vandjac/Logic-PCB/Screenshots/Logic-PCB-Front.png

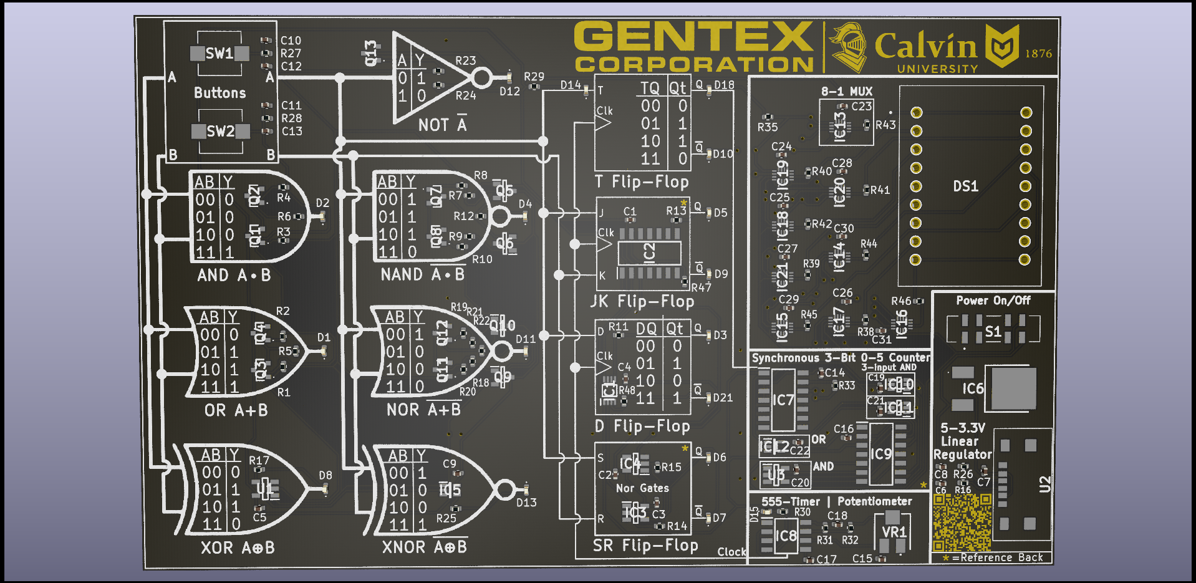
Screenshots/Logic-PCB-Front.png
