vandjac/Logic-PCB/Screenshots/AND.PNG

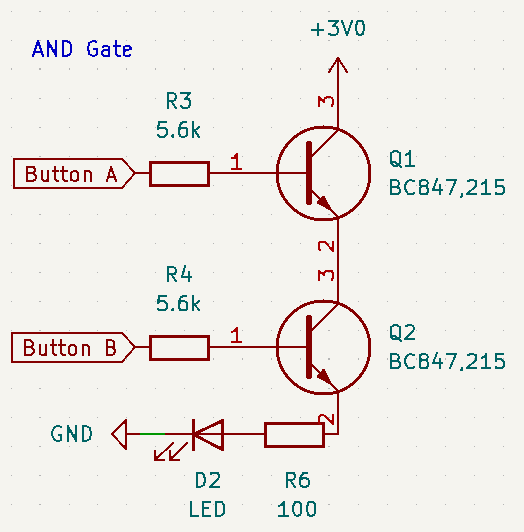
Screenshots/AND.PNG
