vandjac/Logic-PCB/Screenshots/Battery.PNG

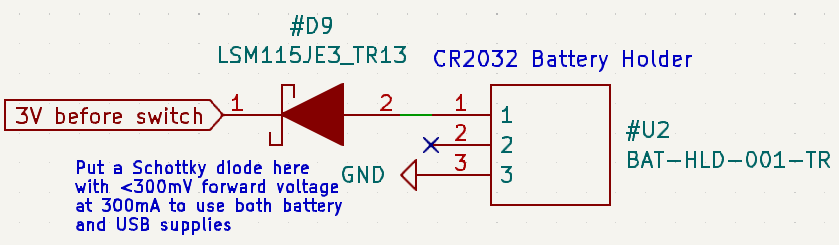
Screenshots/Battery.PNG
