vandjac/Logic-PCB/Screenshots/Buttons.PNG

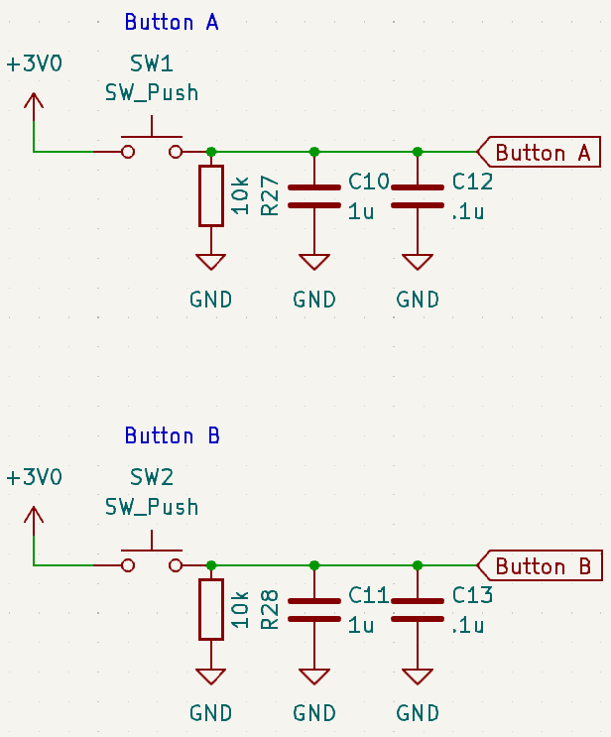
Screenshots/Buttons.PNG
