vandjac/Logic-PCB/Screenshots/Clock.PNG

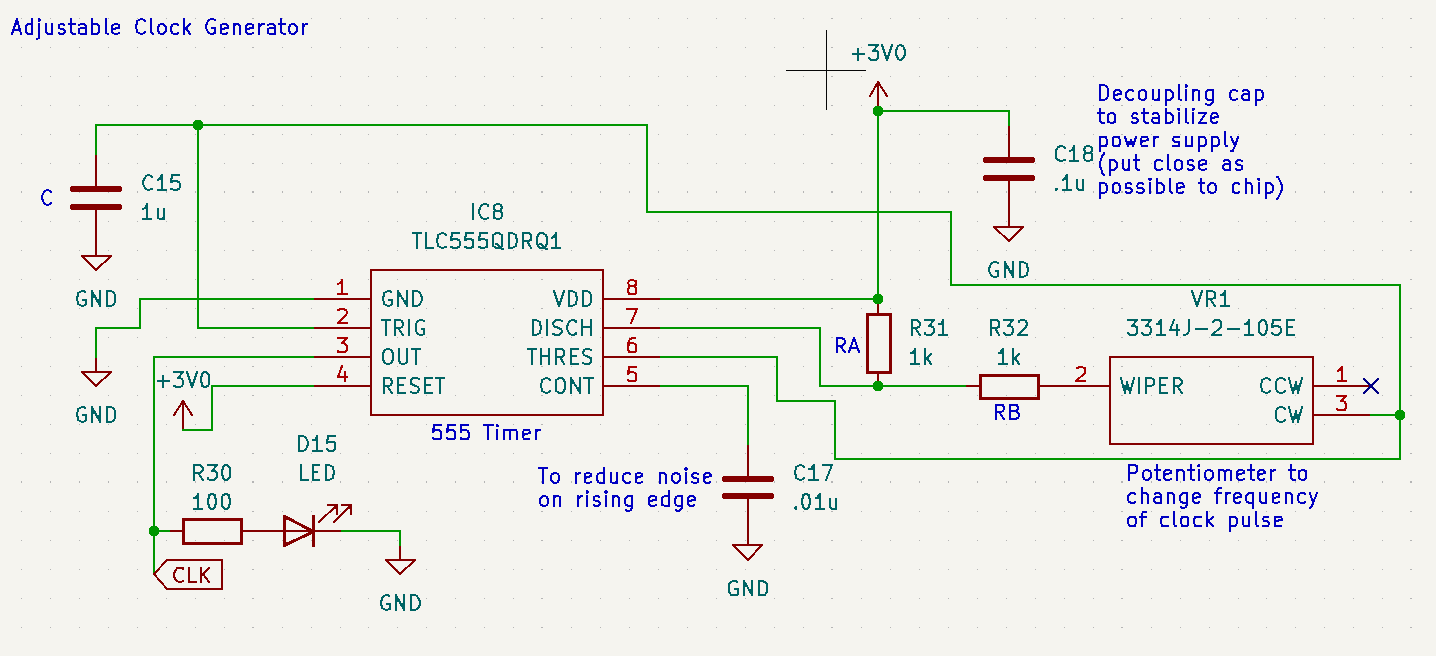
Screenshots/Clock.PNG
