vandjac/Logic-PCB/Screenshots/Counter.PNG

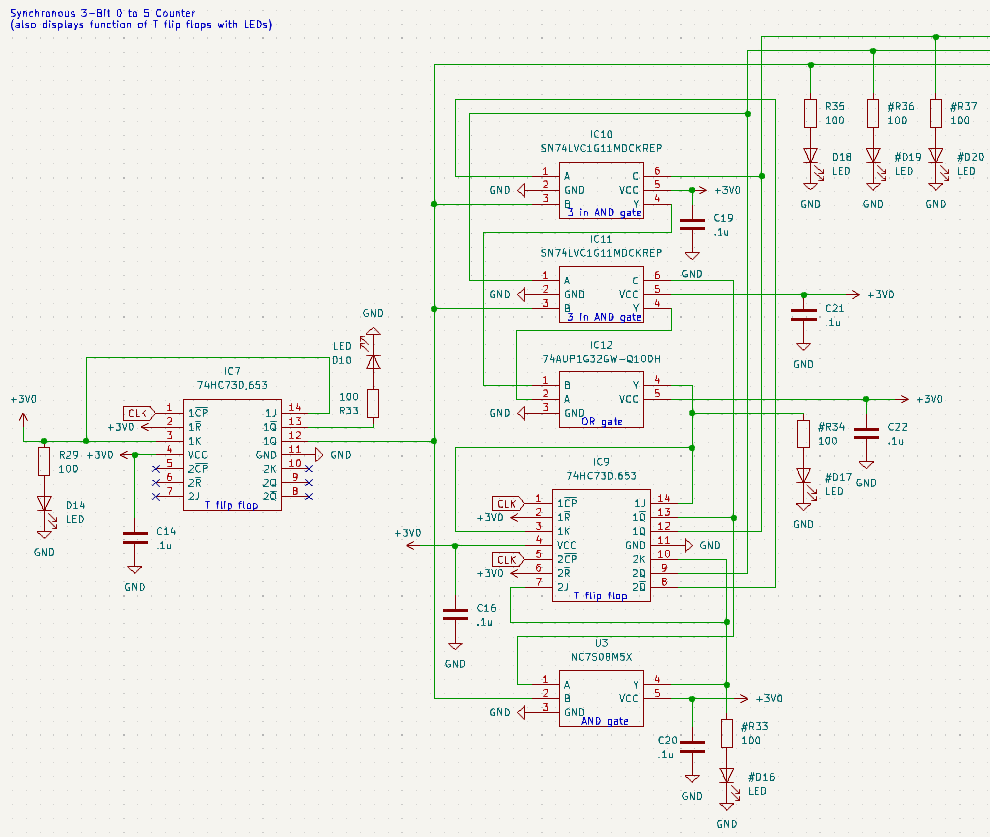
Screenshots/Counter.PNG
