vandjac/Logic-PCB/Screenshots/CounterSim.PNG

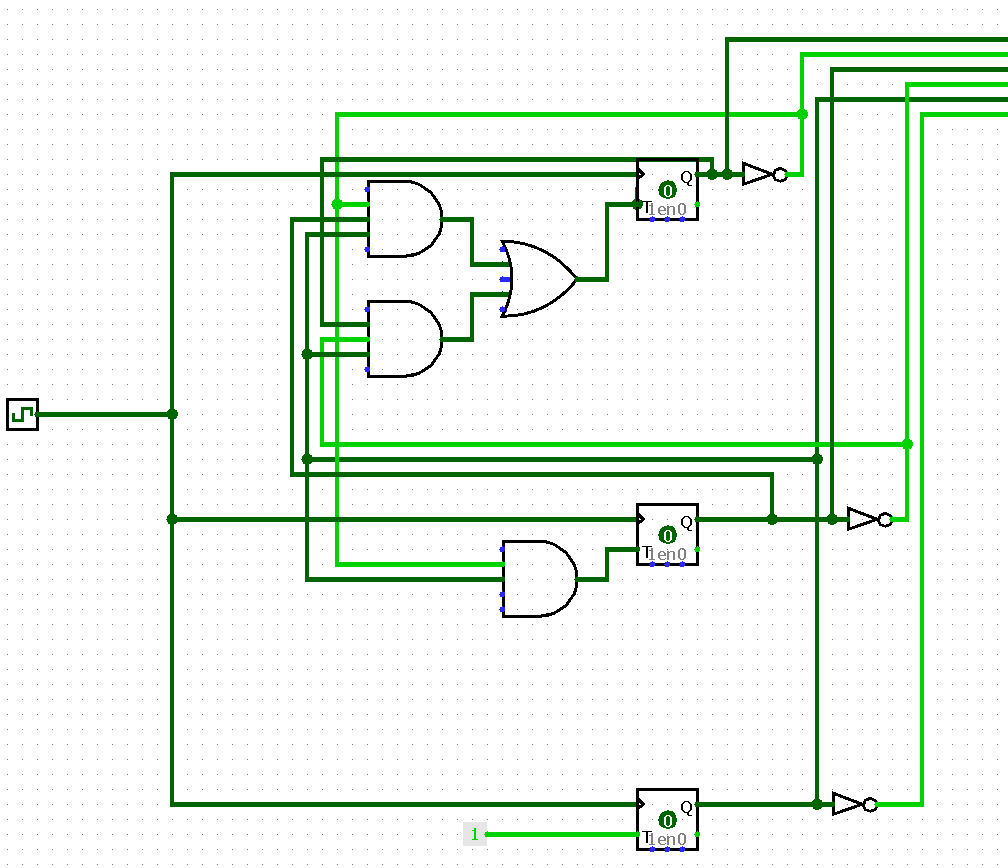
Screenshots/CounterSim.PNG
