vandjac/Logic-PCB/Screenshots/D flip flop.PNG

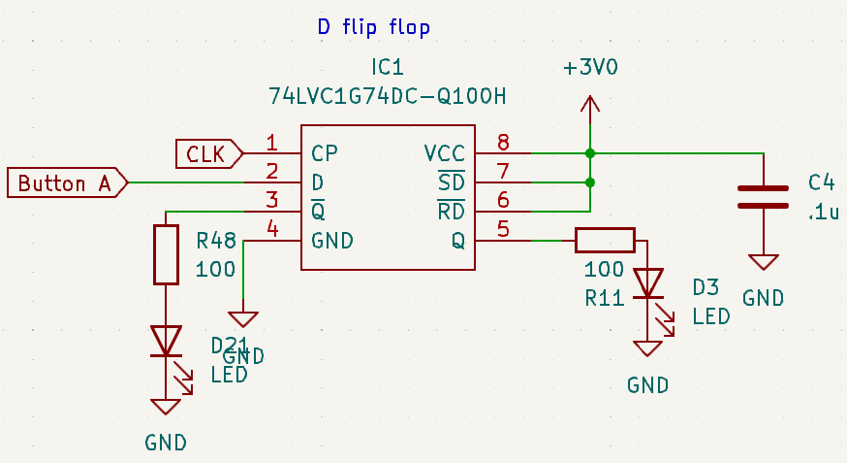
Screenshots/D flip flop.PNG
