vandjac/Logic-PCB/Screenshots/Logic_PCB_Layout_Back.png

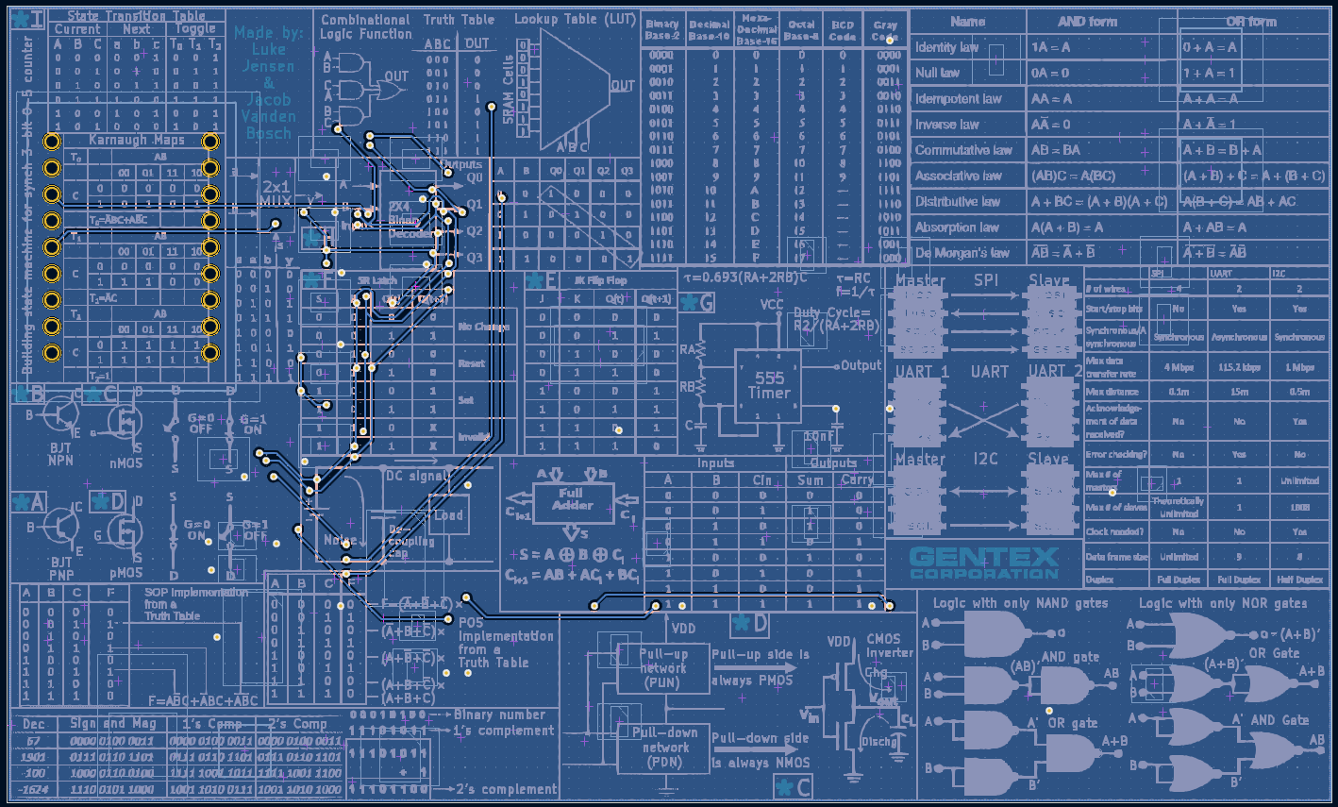
Screenshots/Logic_PCB_Layout_Back.png
