vandjac/Logic-PCB/Screenshots/Logic_PCB_Layout_Front.png

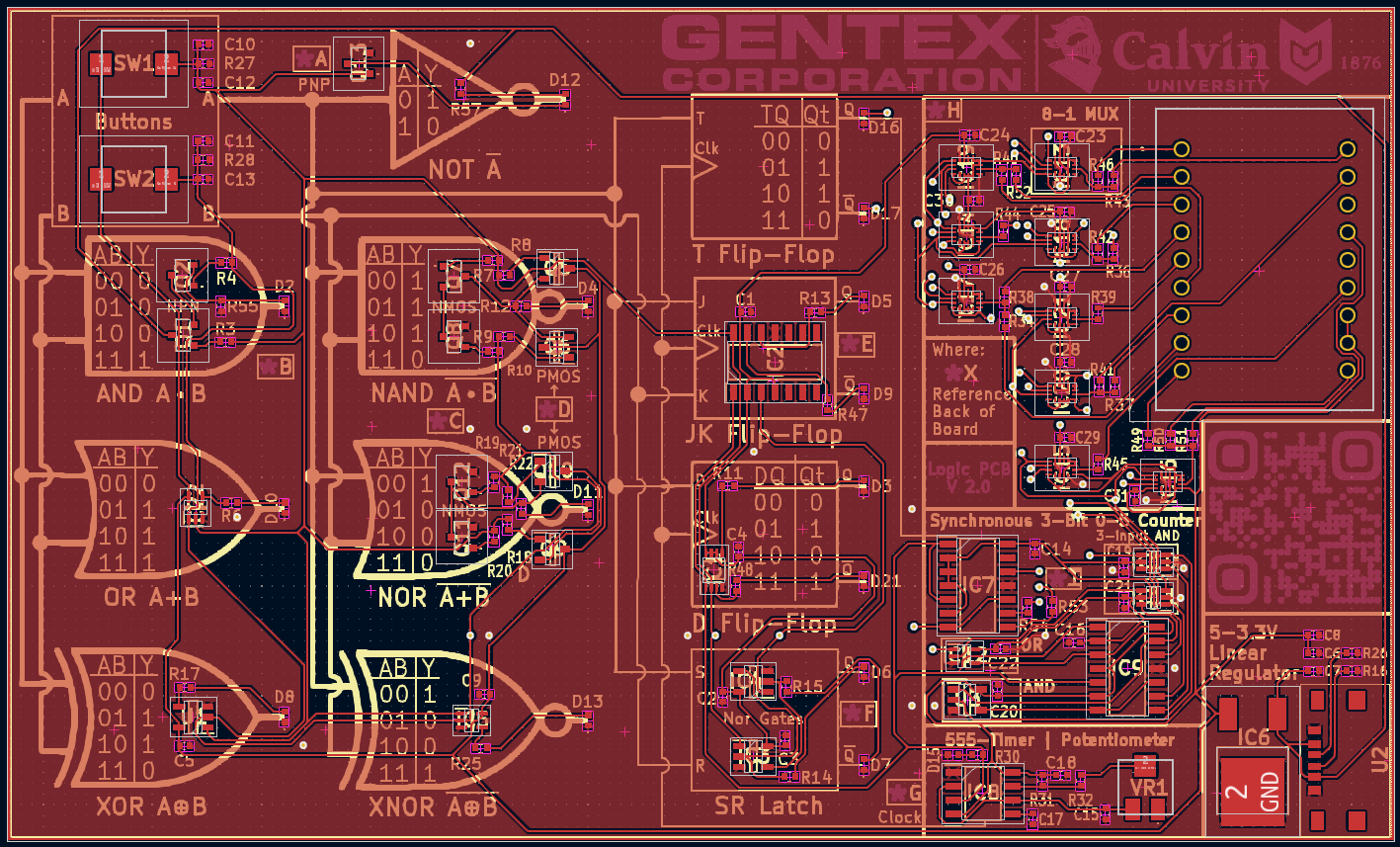
Screenshots/Logic_PCB_Layout_Front.png
