vandjac/Logic-PCB/Screenshots/Logic_PCB_Routing_Back.png

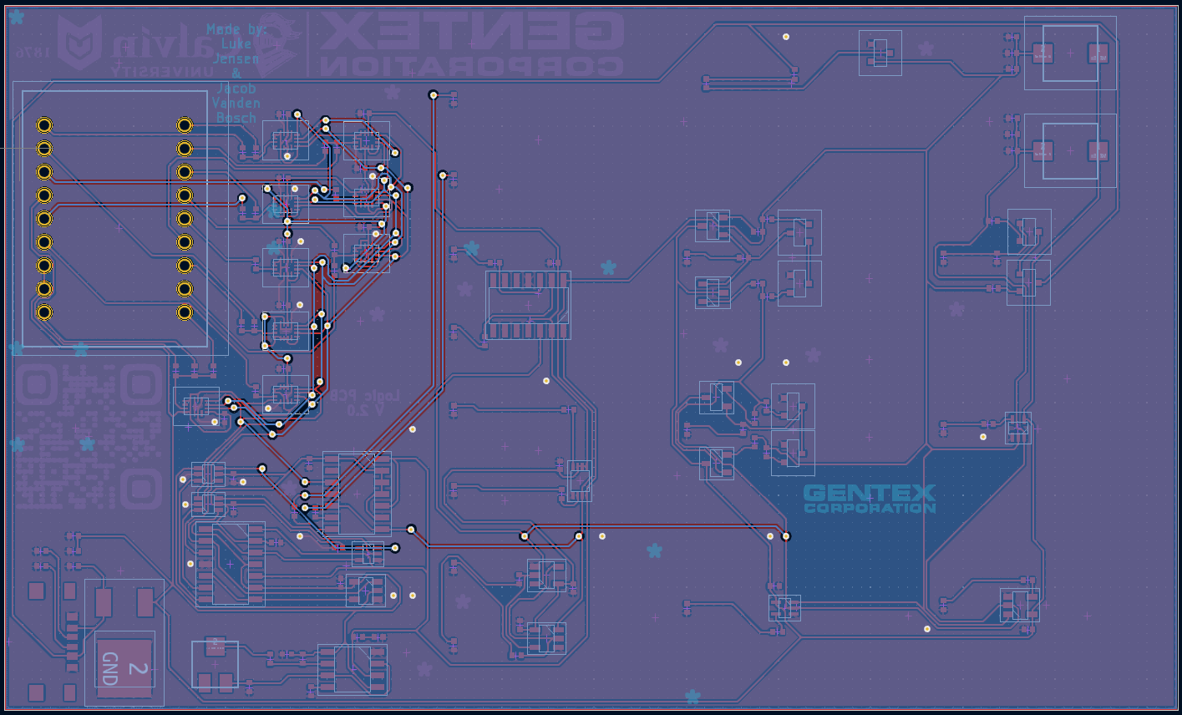
Screenshots/Logic_PCB_Routing_Back.png
