vandjac/Logic-PCB/Screenshots/Logic_PCB_Routing_Front.png

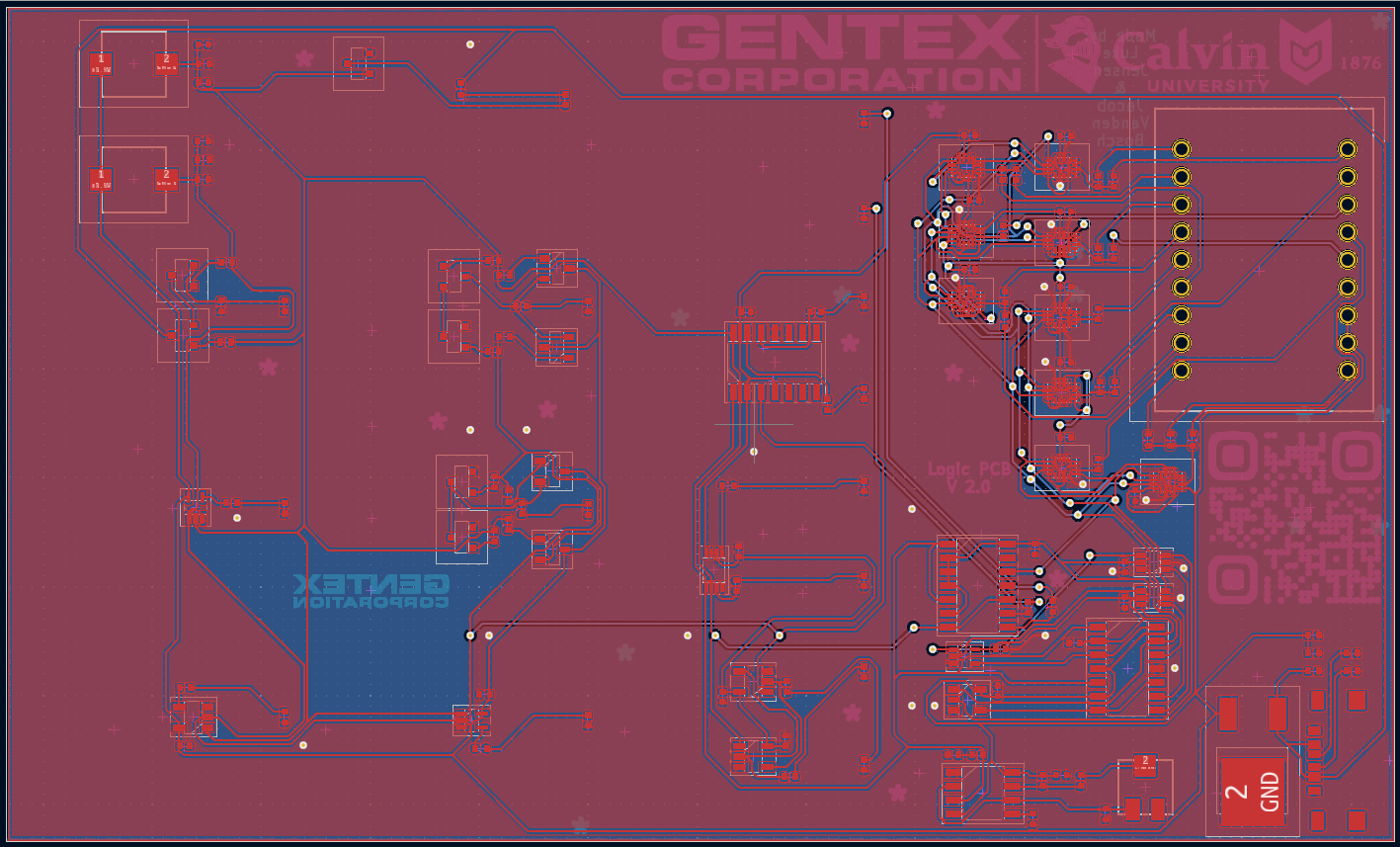
Screenshots/Logic_PCB_Routing_Front.png
