vandjac/Logic-PCB/Screenshots/Muxes.PNG

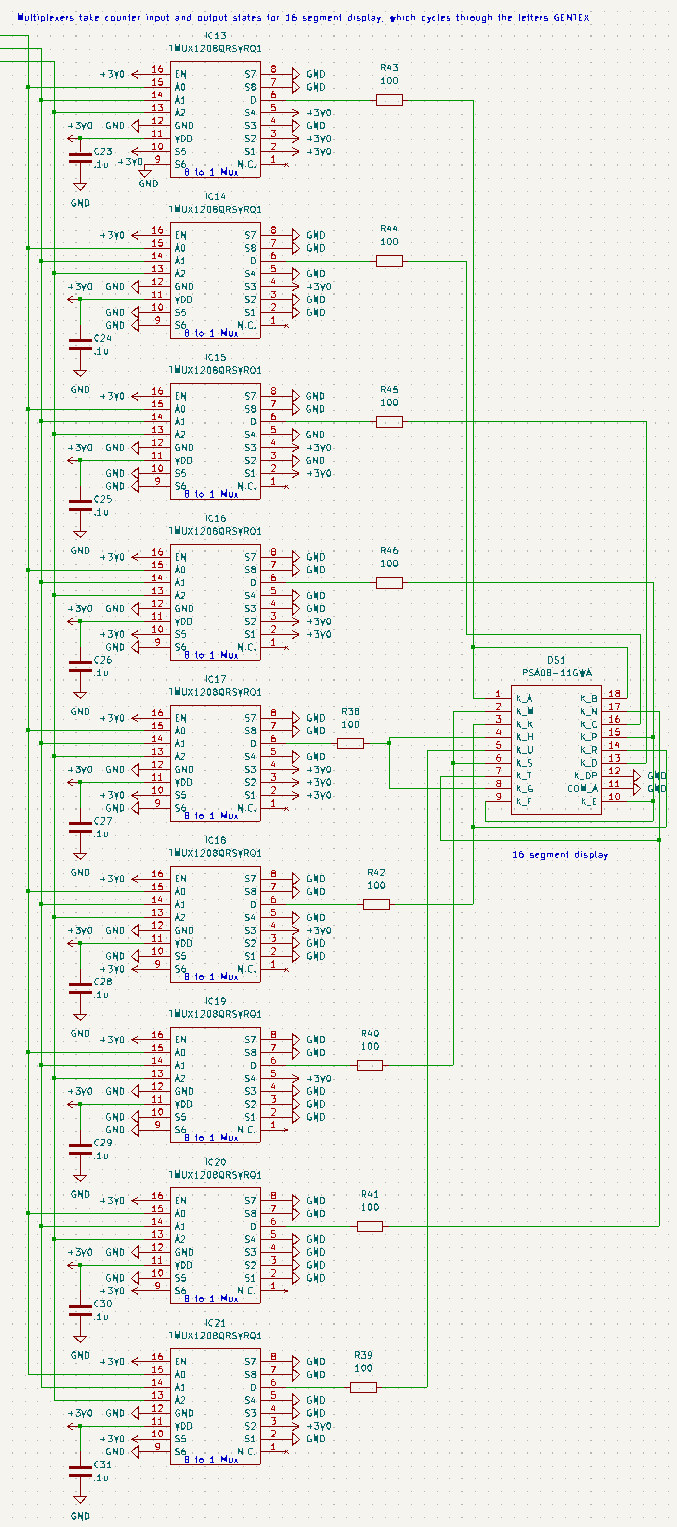
Screenshots/Muxes.PNG
