vandjac/Logic-PCB/Screenshots/NAND.PNG

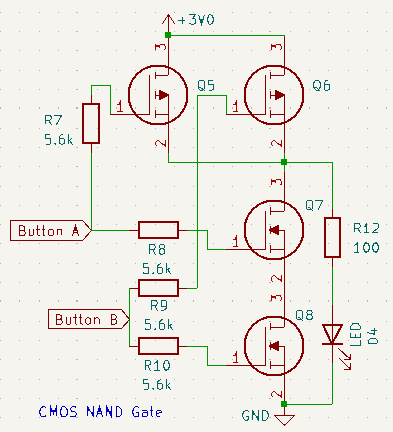
Screenshots/NAND.PNG
