vandjac/Logic-PCB/Screenshots/NOR.PNG

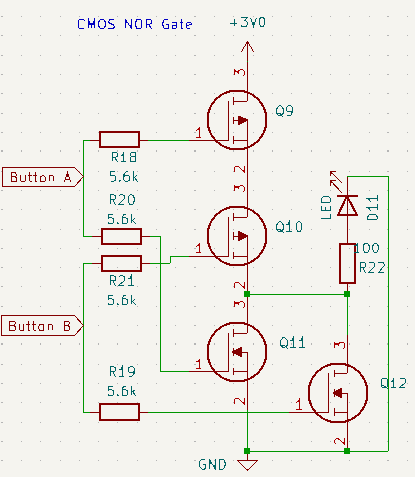
Screenshots/NOR.PNG
