vandjac/Logic-PCB/Screenshots/On Off switch.PNG

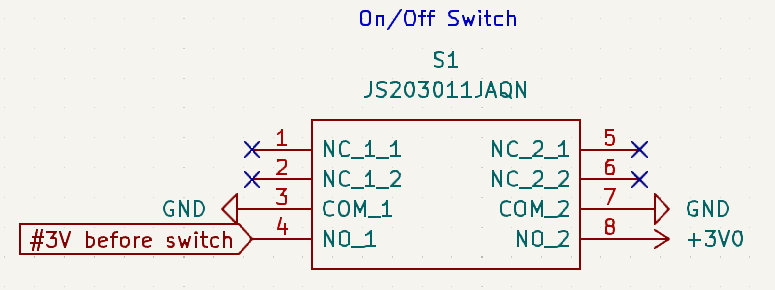
Screenshots/On Off switch.PNG
