vandjac/Logic-PCB/Screenshots/Sim.png

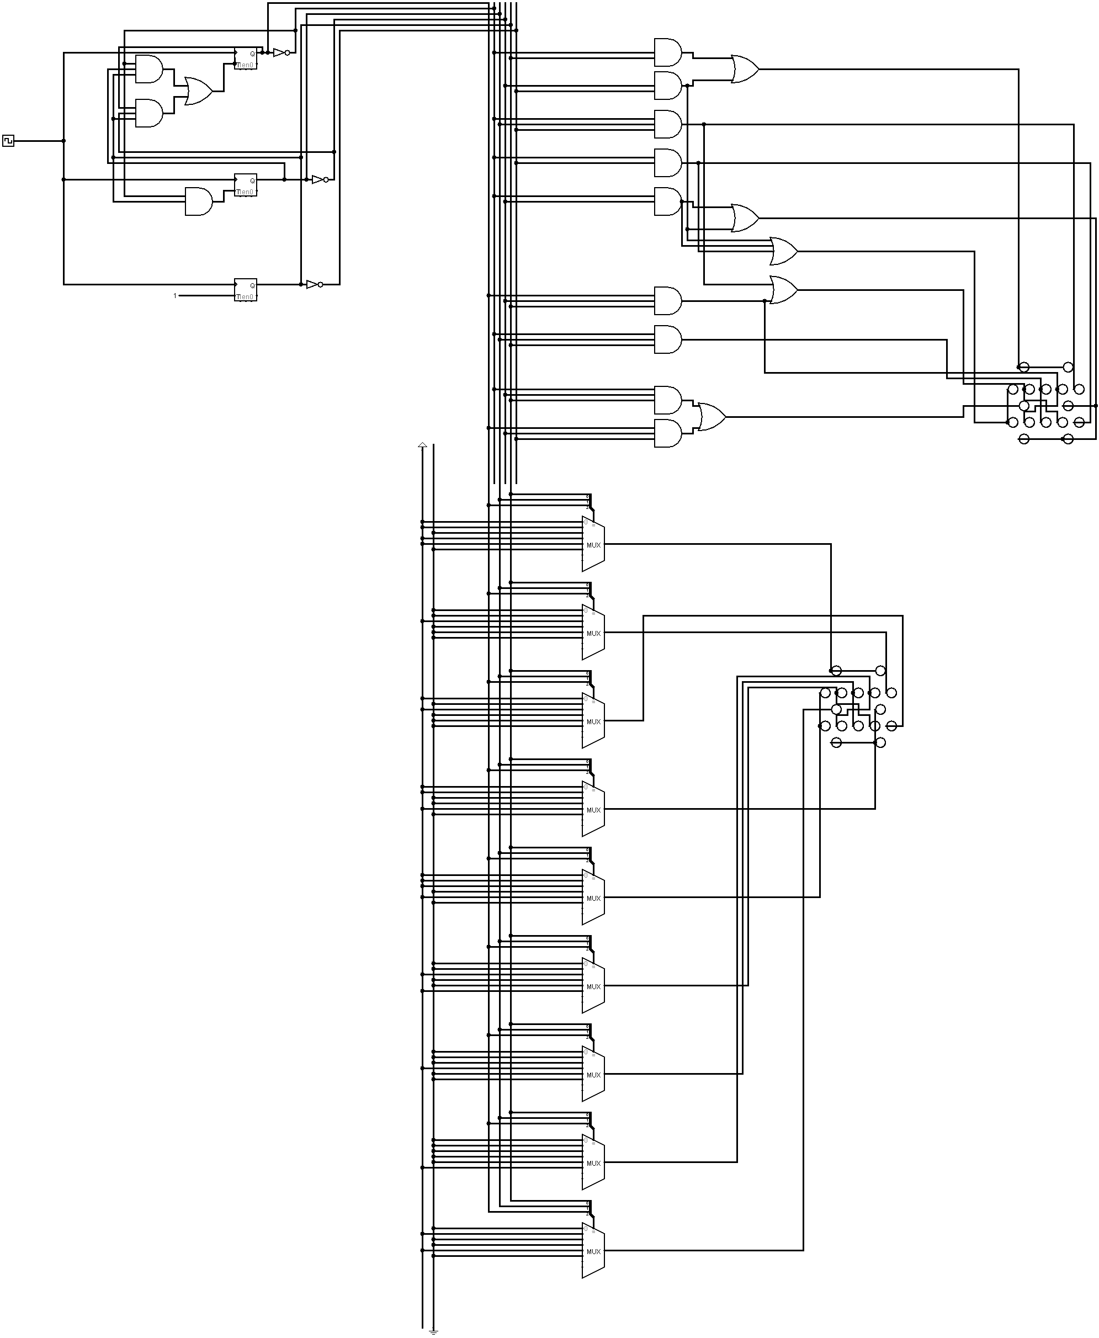
Screenshots/Sim.png
