vandjac/Logic-PCB/Screenshots/SR latch.PNG

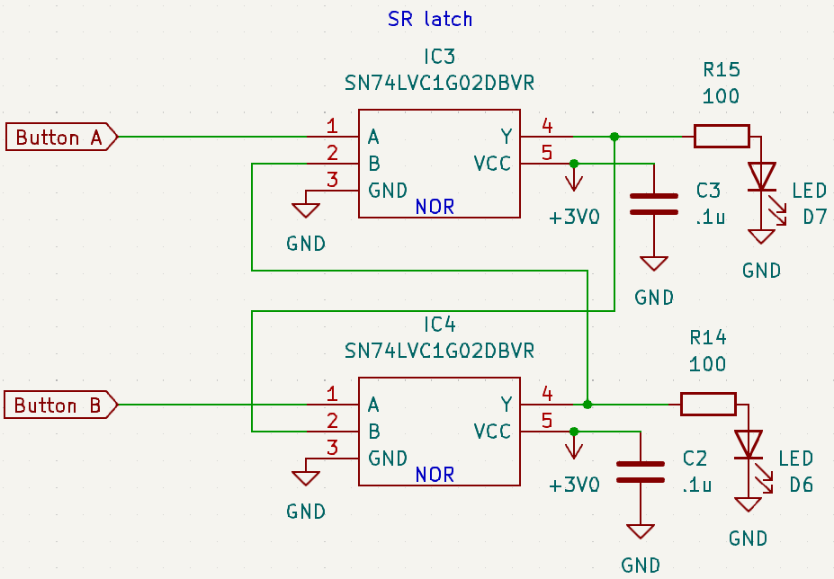
Screenshots/SR latch.PNG
