vandjac/Logic-PCB/Screenshots/T flip flop.PNG

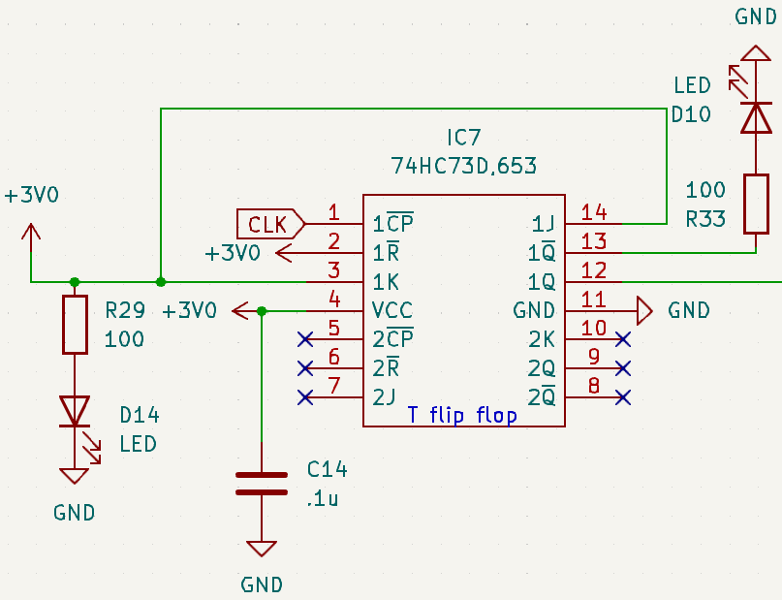
Screenshots/T flip flop.PNG
