vandjac/Logic-PCB/Screenshots/USB C.PNG

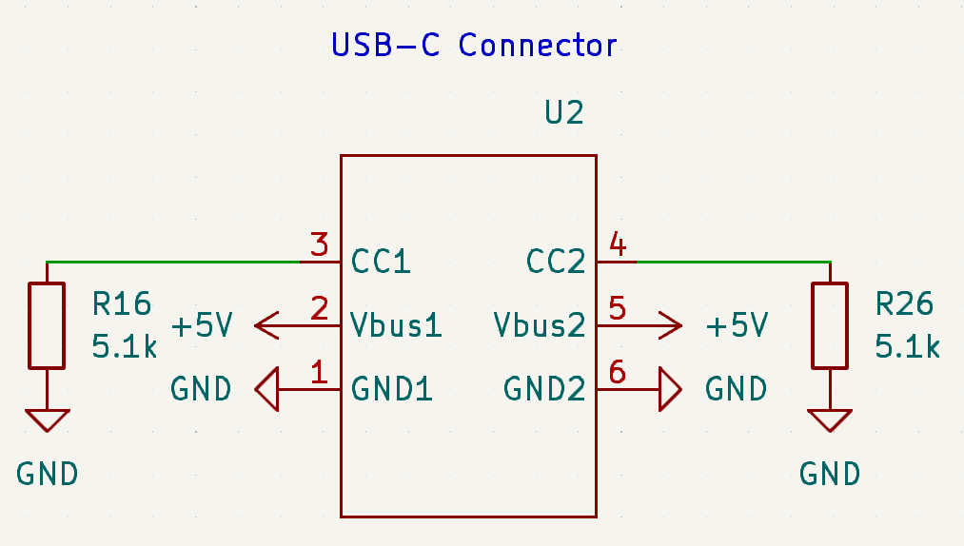
Screenshots/USB C.PNG
