vandjac/Logic-PCB/Screenshots/XOR.PNG

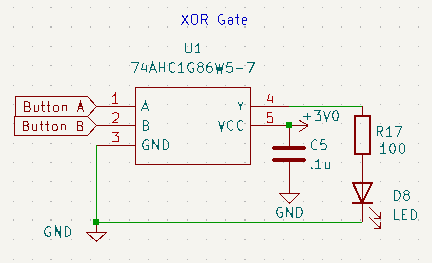
Screenshots/XOR.PNG
